chuxin520922/SmallDesktopDisplay/2.Firmware/源代码/v1.4加气象预警/v1.4加气象预警/SmallDesktopDisplay/img/pangzi_change/QQ截图20210914220035.jpg

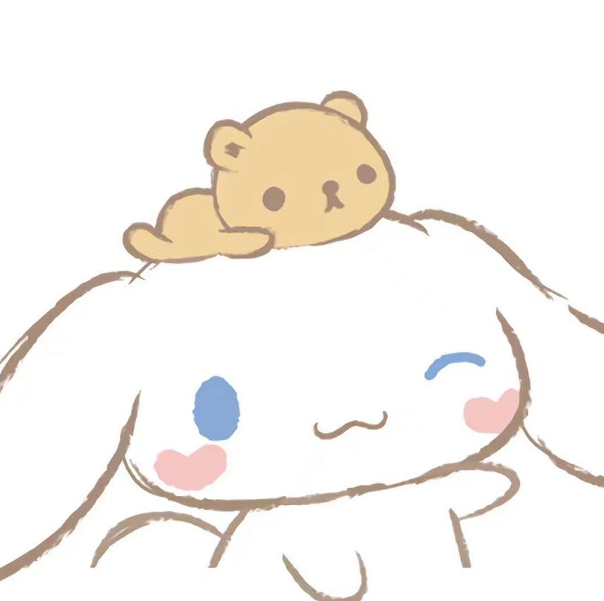
2.Firmware/源代码/v1.4加气象预警/v1.4加气象预警/SmallDesktopDisplay/img/pangzi_change/QQ截图20210914220035.jpg
