chuxin520922/SmallDesktopDisplay/3.Software/字库工具/取字库 - 无特殊需要不需要该步骤/processing-3.5.4/modes/java/examples/Basics/Image/Alphamask/data/mask.jpg

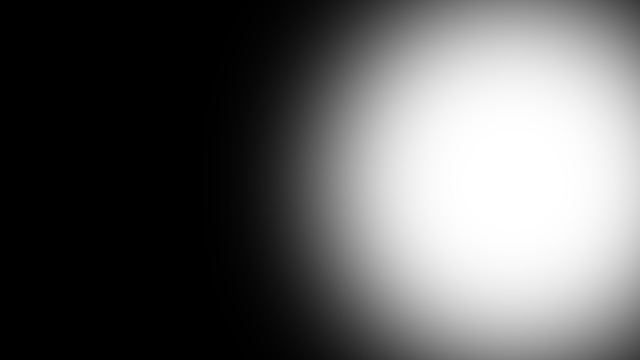
3.Software/字库工具/取字库 - 无特殊需要不需要该步骤/processing-3.5.4/modes/java/examples/Basics/Image/Alphamask/data/mask.jpg
