chuxin520922/SmallDesktopDisplay/3.Software/用PY生成动画头文件/gif_to_h/hutao.gif

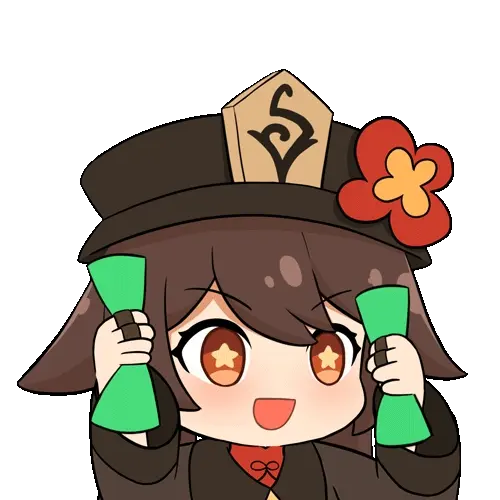
3.Software/用PY生成动画头文件/gif_to_h/hutao.gif
