chuxin520922/SmallDesktopDisplay/5.Docs/图片素材/太空人/misika.jpg

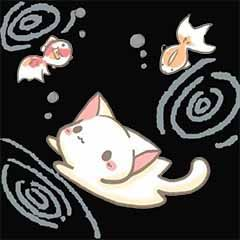
5.Docs/图片素材/太空人/misika.jpg
