chuxin520922/SmallDesktopDisplay/5.Docs/图片素材/太空人/众生之门11.jpg

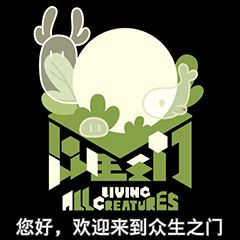
5.Docs/图片素材/太空人/众生之门11.jpg
