chuxin520922/SmallDesktopDisplay/2.Firmware/源代码/1.4.2 SD3 PLUS优化/SmallDesktopDisplay/qr.h

#include <pgmspace.h>  // PROGMEM support header

const unsigned short  qr[] PROGMEM={
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
};
