chuxin520922/SmallDesktopDisplay/2.Firmware/源代码/1.4.2 SD3 PLUS优化/SmallDesktopDisplay/number.h

#ifndef NUMBER_H
#define NUMBER_H

#include <TFT_eSPI.h> 

#include "font/O_3660_i0.h"
#include "font/O_3660_i1.h"
#include "font/O_3660_i2.h"
#include "font/O_3660_i3.h"
#include "font/O_3660_i4.h"
#include "font/O_3660_i5.h"
#include "font/O_3660_i6.h"
#include "font/O_3660_i7.h"
#include "font/O_3660_i8.h"
#include "font/O_3660_i9.h"

#include "font/W_3660_i0.h"
#include "font/W_3660_i1.h"
#include "font/W_3660_i2.h"
#include "font/W_3660_i3.h"
#include "font/W_3660_i4.h"
#include "font/W_3660_i5.h"
#include "font/W_3660_i6.h"
#include "font/W_3660_i7.h"
#include "font/W_3660_i8.h"
#include "font/W_3660_i9.h"

#include "font/W_1830_i0.h"
#include "font/W_1830_i1.h"
#include "font/W_1830_i2.h"
#include "font/W_1830_i3.h"
#include "font/W_1830_i4.h"
#include "font/W_1830_i5.h"
#include "font/W_1830_i6.h"
#include "font/W_1830_i7.h"
#include "font/W_1830_i8.h"
#include "font/W_1830_i9.h"


class Number
{
private:


public:
  //void init();
  void printfW3660(int numx,int numy,int numn);
  void printfO3660(int numx,int numy,int numn);
  void printfW1830(int numx,int numy,int numn);
};


#endif
