chuxin520922/SmallDesktopDisplay/2.Firmware/源代码/1.4.2 SD3 PLUS优化/SmallDesktopDisplay/weathernum.h

#ifndef WEATHERNUM_H
#define WEATHERNUM_H

#include <TFT_eSPI.h> 

#include "img/tianqi/t0.h"
#include "img/tianqi/t1.h"
#include "img/tianqi/t2.h"
#include "img/tianqi/t3.h"
#include "img/tianqi/t4.h"
#include "img/tianqi/t5.h"
#include "img/tianqi/t6.h"
#include "img/tianqi/t7.h"
#include "img/tianqi/t9.h"
#include "img/tianqi/t11.h"
#include "img/tianqi/t13.h"
#include "img/tianqi/t14.h"
#include "img/tianqi/t15.h"
#include "img/tianqi/t16.h"
#include "img/tianqi/t18.h"
#include "img/tianqi/t19.h"
#include "img/tianqi/t20.h"
#include "img/tianqi/t26.h"
#include "img/tianqi/t29.h"
#include "img/tianqi/t30.h"
#include "img/tianqi/t31.h"
#include "img/tianqi/t53.h"
#include "img/tianqi/t99.h"


class WeatherNum
{
private:


public:
  void printfweather(int numx,int numy,int numw);
};


#endif
